Kinben-Electronics-Team/Kinben-Unified-Parts-Reference-System/.agent-work/task-0.3-integration.md

# TASK 0.3: SYSTEM INTEGRATION AUDIT - Assembly-System-Component Relationships

## Systems Tab HTML Structure (Lines 867-945)

### System Form Elements
- **Lines 872-888**: Metadata form (name, version, status, description)
- **Lines 895-921**: System items form
  - Item type selector: assembly/mechanical/printed3d/cable/system
  - Dynamic item dropdown (populated by `updateSystemItemOptions()`)
  - Quantity input (minimum 1)
  - Add Item button

### System Display Elements
- **Line 923**: `<div id="system-items">` - Current system items container
- **Lines 925-928**: Action buttons (Add System, Export CSV)
- **Line 930**: Search box for systems filtering
- **Lines 932-944**: Systems table with sortable columns

## Systems JavaScript Function Architecture

### Core System Management
- **`addSystemItem()`**: Adds items to current system-in-progress
- **`removeSystemItem(index)`**: Removes items from current system
- **`renderSystemItems()`**: Displays current system items during creation
- **`addSystem()`**: Saves complete system to `data.systems` array
- **`updateSystemItemOptions()`**: Populates item dropdown based on selected type

### System Display & Interaction
- **`renderSystems()`**: Renders all systems in main table
- **`sortSystems(column)`**: Sorts systems table by specified column
- **`filterSystems()`**: Search filter functionality
- **`exportSystems()`**: CSV export for systems data

## Three-Tier Architecture Data Flow

```
TIER 1: Components (KPN-based identification)
├── Electronic components (resistors, capacitors, ICs, etc.)
├── Mechanical parts (enclosures, screws, standoffs)
├── 3D-printed parts (custom housings, brackets)
└── Cable assemblies (harnesses, connectors)
    ↓ Referenced by KPN strings
    
TIER 2: Assemblies (Name-based identification)  
├── PCB assemblies with BOMs (component lists)
├── Cable assemblies (connector + wire specifications)
└── Mechanical assemblies (hardware groupings)
    ↓ Referenced by name strings
    
TIER 3: Systems (Name-based hierarchy)
├── Product-level systems (complete devices)
├── Sub-systems (functional blocks)
└── System-of-systems (nested hierarchies)
```

## System Item Types and Referencing Mechanisms

### Five System Item Types
1. **assembly**: References `data.assemblies` by name matching
2. **mechanical**: References components where `category='mechanical'` by KPN
3. **printed3d**: References components where `category='printed3d'` by KPN  
4. **cable**: References components where `category='cable'` by KPN
5. **system**: References other systems by name (enables hierarchical nesting)

### Reference Resolution Logic
```javascript
// Assembly references (by name)
assembly = data.assemblies.find(a => a.name === itemValue)

// Component references (by KPN)  
component = data.components.find(c => c.kpn === itemValue)

// System references (by name - hierarchical)
system = data.systems.find(s => s.name === itemValue)
```

## System Data Structure

### Complete System Object
```javascript
system = {
    name: "IoT Environmental Monitor",        // Unique system identifier
    version: "v1.0",                         // Version tracking
    status: "Active",                        // Active/Inactive status
    description: "Complete monitoring system", // System purpose
    items: [                                 // Array of system items
        {
            type: "assembly",                // Item type classifier
            value: "Main Controller Board", // Assembly name reference
            name: "Main Controller Board",  // Display name
            version: "v2.1",               // Assembly version (for display)
            quantity: 1                     // Quantity in system
        },
        {
            type: "mechanical",             // Component-based item
            value: "MEC-ENC-001",          // Component KPN reference
            name: "MEC-ENC-001",           // Component KPN (display)
            version: "Aluminum Enclosure", // Component description
            quantity: 1                    // Quantity in system
        }
    ],
    dateAdded: "2025-01-15T10:30:00.000Z"   // Creation timestamp
}
```

### Backward Compatibility Handling
- **Legacy Format**: `system.pcbs` array (deprecated)
- **Current Format**: `system.items` array
- **Migration**: Automatic conversion during data load
- **Display**: Handles both formats transparently

## Component-Assembly Relationship

### Assembly BOM Structure
```javascript
assembly = {
    name: "Main Controller Board",
    version: "v2.1", 
    status: "Active",
    description: "ARM-based controller",
    bom: [                              // Bill of Materials
        {
            kpn: "RES-STD-001",         // Component KPN reference
            componentName: "10kΩ Resistor", // Resolved component name
            quantity: 4,                // Quantity per assembly
            refdes: "R1,R2,R3,R4"      // Reference designators
        },
        {
            kpn: "CAP-CER-001",
            componentName: "100nF Capacitor",
            quantity: 2,
            refdes: "C1,C2"
        }
    ]
}
```

### Component Validation in BOMs
- **KPN Cross-Reference**: BOM items validate against `data.components`
- **CSV Import Validation**: Papa Parse system checks KPN existence
- **Missing KPN Handling**: Import preview shows validation errors
- **Real-time Updates**: Component changes reflect in assembly displays

## Assembly-System Relationship

### System Assembly References
```javascript
// System references assembly by name
systemItem = {
    type: "assembly",
    value: "Main Controller Board",    // Must match assembly.name exactly
    name: "Main Controller Board",     // Display name (same as value)
    version: "v2.1",                  // Assembly version (for display)
    quantity: 2                       // Quantity of this assembly in system
}

// Lookup mechanism
referencedAssembly = data.assemblies.find(a => a.name === systemItem.value)
```

### Assembly Selection Logic
- **Active Only**: Only assemblies with `status: "Active"` appear in dropdown
- **Name-based**: References use assembly name (not ID or KPN)
- **Version Display**: Assembly version shown for reference but not part of lookup
- **Quantity Management**: System-level quantities independent of assembly BOMs

## Data Storage and Persistence

### localStorage Structure
**Storage Key**: `'kinben-simple-data'`
```javascript
data = {
    components: [                       // Component library (KPN-indexed)
        { kpn: "RES-STD-001", category: "resistors", ... },
        { kpn: "CAP-CER-001", category: "capacitors", ... }
    ],
    assemblies: [                       // Assembly definitions (name-indexed)
        { name: "Main Controller", bom: [...], ... },
        { name: "Power Supply", bom: [...], ... }
    ],
    systems: [                          // System hierarchy (name-indexed)
        { name: "IoT Monitor", items: [...], ... },
        { name: "Control System", items: [...], ... }
    ],
    vendors: ["Mouser", "Digi-Key", ...]  // Vendor dropdown options
}
```

### CSV Integration Status
**Current CSV Support**:
- ✅ **Components**: Full read/write via 16 CSV files in `csvFileMap`
- ❌ **Assemblies**: Export only (`exportAssemblies()` function)
- ❌ **Systems**: Export only (`exportSystems()` function)

**Missing CSV Files**:
- No `ASSEMBLIES.csv` in `csvFileMap` 
- No `SYSTEMS.csv` in `csvFileMap`
- Systems and Assemblies persist to localStorage only

## Integration Validation Points

### System Item Validation
1. **Type Validation**: Ensures item type matches available options
2. **Reference Validation**: Checks existence of referenced assemblies/components
3. **Status Validation**: Only active assemblies/components selectable
4. **Quantity Validation**: Minimum 1, integer values only

### Cross-Reference Integrity
```javascript
// Assembly → Component validation (in BOM)
bomItem.kpn exists in data.components.map(c => c.kpn)

// System → Assembly validation (in items)
systemItem.value exists in data.assemblies.filter(a => a.status === 'Active').map(a => a.name)

// System → Component validation (mechanical/3d/cable items)
systemItem.value exists in data.components.filter(c => c.category === itemType).map(c => c.kpn)
```

### Data Migration and Compatibility
- **Automatic Migration**: Converts legacy `system.pcbs` to `system.items`
- **Version Handling**: Maintains version info across all tiers
- **Status Propagation**: Inactive items excluded from selection but preserved in data
- **Export Compatibility**: CSV exports handle both legacy and current formats

## System Hierarchy Architecture

### Hierarchical Nesting Support
```javascript
// System can contain other systems
systemItem = {
    type: "system",
    value: "Sub-Control Module",       // References another system by name
    name: "Sub-Control Module", 
    version: "v1.3",
    quantity: 1
}
```

### Circular Reference Prevention
- **Current Status**: No automatic circular reference detection
- **Manual Prevention**: User responsibility to avoid circular references
- **Future Enhancement**: Validation system needed for complex hierarchies

## Assessment Summary

**Current Integration Status**:
- ✅ **Component-Assembly**: Full KPN-based referencing with CSV import validation
- ✅ **Assembly-System**: Complete name-based referencing with active status filtering
- ✅ **Data Persistence**: Unified localStorage system with backward compatibility
- ✅ **Export Capabilities**: CSV export for all data types
- ⚠️ **CSV Sync**: Limited to components only (assemblies/systems localStorage only)
- ⚠️ **Circular References**: No validation for system hierarchies

**Architecture Strengths**:
- Clear three-tier hierarchy with distinct referencing mechanisms
- Flexible item type system supporting diverse product structures
- Robust validation and error handling at integration points
- Backward compatibility with legacy data formats
- Real-time updates across all integration points

**Ready for Enhancement**: 
- Modular architecture supports easy extension to new item types
- Clear separation of concerns between tiers
- Extensible validation system for new requirements
- Foundation prepared for advanced hierarchy features

**No Code Modifications Made**: Assessment only - all functionality remains unchanged.
