Kinben-Electronics-Team/Kinben-Unified-Parts-Reference-System/.agent-work/task-1.3-data-model.md

# TASK 1.3: EXTEND DATA MODEL

## Implementation Progress

**Objective**: Update assembly objects to include type and type-specific data  
**Status**: COMPLETE - All code changes implemented  
**Date**: 2025-07-31  

## Code Changes Made

### Data Collection Enhancement (Lines 3377-3379)
**Function**: `addAssembly()` - Extended to collect cable-specific data

```javascript
// Collect cable-specific data if cable assembly
const cableLength = document.getElementById('cableLength').value;
const cableType = document.getElementById('cableType').value;
```

**Features**:
- Collects cable length and type values from form fields
- Values collected regardless of assembly type (form handles visibility)
- Prepared for conditional storage based on assembly type

### Extended Assembly Object Structure (Lines 3386-3404)
**Updated Data Model**: Assembly objects now include type-specific data containers

```javascript
const assembly = {
    name,
    type: assemblyType,  // 'pcb' or 'cable'
    version,
    status,
    description,
    // Type-specific data
    pcbData: assemblyType === 'pcb' ? {
        bom: [...currentBOM]
    } : null,
    cableData: assemblyType === 'cable' ? {
        length: cableLength ? parseInt(cableLength) : null,
        cableType: cableType || null,
        bom: [...currentBOM]
    } : null,
    // Legacy field for backward compatibility
    bom: [...currentBOM],
    dateAdded: new Date().toISOString().split('T')[0]
};
```

**Data Model Features**:
- **Type-Specific Storage**: PCB data stored in `pcbData`, cable data in `cableData`
- **Conditional Creation**: Only relevant data object created based on assembly type
- **Data Validation**: Cable length converted to integer, handles empty values
- **Backward Compatibility**: Legacy `bom` field maintained for existing code
- **BOM Duplication**: BOM stored in both type-specific and legacy locations

### Data Migration Logic (Lines 1903-1919)
**Function**: `loadData()` - Automatic migration for existing assemblies

```javascript
// Migrate assemblies to include type field (default to PCB)
if (data.assemblies) {
    let migrationNeeded = false;
    data.assemblies.forEach(assembly => {
        if (!assembly.type) {
            assembly.type = 'pcb'; // Default existing assemblies to PCB type
            assembly.pcbData = {
                bom: assembly.bom || []
            };
            assembly.cableData = null;
            migrationNeeded = true;
        }
    });
    if (migrationNeeded) {
        saveData();
    }
}
```

**Migration Features**:
- **Automatic Detection**: Identifies assemblies without type field
- **PCB Default**: Existing assemblies default to PCB type (safest assumption)
- **Data Structure Creation**: Creates pcbData object with existing BOM
- **Null Cable Data**: Sets cableData to null for migrated PCB assemblies
- **Efficient Saving**: Only saves data if migration was actually needed
- **One-Time Process**: Migration runs once per legacy assembly

## Data Structure Specifications

### PCB Assembly Data Structure
```javascript
{
    name: "Main Controller Assembly",
    type: "pcb",
    version: "v1.0",
    status: "Active",
    description: "ARM-based controller board",
    pcbData: {
        bom: [...bomItems]  // Array of BOM items
    },
    cableData: null,
    bom: [...bomItems],  // Legacy compatibility
    dateAdded: "2025-07-31"
}
```

### Cable Assembly Data Structure
```javascript
{
    name: "Main Power Cable",
    type: "cable",
    version: "v1.0", 
    status: "Active",
    description: "Power distribution cable assembly",
    pcbData: null,
    cableData: {
        length: 500,           // Length in mm (integer)
        cableType: "18 AWG",   // Cable type specification
        bom: [...bomItems]     // Array of BOM items (connectors, etc.)
    },
    bom: [...bomItems],  // Legacy compatibility
    dateAdded: "2025-07-31"
}
```

### Legacy Assembly (Migrated) Structure
```javascript
{
    name: "Legacy PCB Assembly",
    type: "pcb",           // Added by migration
    version: "v1.0",
    status: "Active", 
    description: "Pre-migration assembly",
    pcbData: {             // Added by migration
        bom: [...bomItems] // Copied from legacy bom field
    },
    cableData: null,       // Added by migration
    bom: [...bomItems],    // Original legacy field preserved
    dateAdded: "2025-07-30"
}
```

## Validation Requirements

### Success Criteria Progress
- [x] New assembly objects include type field
- [x] Type-specific data stored appropriately (pcbData/cableData)
- [x] Existing assemblies migrated successfully (default to PCB)
- [x] CSV sync includes new fields (handled by saveData)
- [x] Data integrity maintained throughout

## Technical Implementation Features

### Type-Specific Data Storage
- **PCB Assemblies**: BOM stored in `pcbData.bom`
- **Cable Assemblies**: BOM + cable specs stored in `cableData`
- **Efficient Storage**: Only relevant data object created per type
- **Data Validation**: Cable length parsed as integer with null fallback

### Backward Compatibility Strategy
- **Legacy BOM Field**: Maintained in all assemblies for existing code
- **Migration Logic**: Automatically updates existing data structures
- **Default Behavior**: Unknown assemblies default to PCB type
- **Preservation**: All existing data preserved during migration

### Data Persistence Integration
- **localStorage Sync**: Extended data model saved to localStorage
- **CSV Integration**: Type-specific data included in CSV exports
- **Migration Persistence**: Migration changes saved automatically
- **Performance**: Migration only runs when needed

## Migration Testing Scenarios

### Scenario 1: Fresh Installation
- **Behavior**: New assemblies created with full type-specific data model
- **PCB Assembly**: Creates pcbData object, cableData null
- **Cable Assembly**: Creates cableData object, pcbData null

### Scenario 2: Existing Data Migration
- **Detection**: Assemblies without type field automatically detected
- **Default Assignment**: All legacy assemblies become PCB type
- **Data Migration**: BOM data moved to pcbData.bom structure
- **Preservation**: Original bom field maintained for compatibility

### Scenario 3: Mixed Data Environment
- **Handling**: New and migrated assemblies coexist seamlessly
- **Consistency**: All assemblies have consistent data structure after migration
- **Functionality**: Both old and new assemblies work with existing code

## Status: TASK 1.3 COMPLETE
✅ Assembly objects extended with type field  
✅ Type-specific data containers implemented (pcbData/cableData)  
✅ Data collection from form fields integrated  
✅ Migration logic for existing assemblies implemented  
✅ Backward compatibility maintained with legacy bom field  
✅ Data persistence and CSV sync compatible  
✅ One-time migration process efficient and safe  
✅ Ready for Task 1.4 - Enhance BOM CSV Import
