Kinben-Electronics-Team/Kinben-Unified-Parts-Reference-System/.agent-work/task-2.2-mother-view.md

# TASK 2.2: IMPLEMENT MOTHER VIEW COMPONENTS

## Implementation Progress

**Objective**: Add manual component entry at assembly level for enclosures, hardware, and other components  
**Status**: COMPLETE - Assembly-level component system implemented  
**Date**: 2025-07-31  

## Code Changes Made

### Assembly Form UI Enhancement (Lines 940-971)
**Location**: Added after BOM CSV Import section, before action buttons

```html
<h3>🏗️ Assembly-Level Components</h3>
<p>Add enclosures, hardware, and other components needed at the assembly level</p>

<div class="form-grid">
    <div class="form-group">
        <label>Component Type</label>
        <select id="mother-type" onchange="updateMotherItemOptions()">
            <option value="">Select Component Type</option>
            <option value="enclosure">Enclosure/Housing</option>
            <option value="hardware">Hardware (Screws, Standoffs)</option>
            <option value="mounting">Mounting Components</option>
            <option value="cable">External Cables</option>
            <option value="other">Other</option>
        </select>
    </div>
    <div class="form-group">
        <label>Component KPN</label>
        <select id="mother-kpn" onchange="updateMotherComponentName()">
            <option value="">Select Component Type First</option>
        </select>
    </div>
    <div class="form-group">
        <label>Quantity</label>
        <input type="number" id="mother-quantity" min="1" value="1">
    </div>
    <div class="form-group">
        <label>Notes</label>
        <input type="text" id="mother-notes" placeholder="Optional notes">
    </div>
</div>
<button class="btn btn-secondary" onclick="addMotherComponent()">Add Assembly Component</button>
```

**UI Design Features**:
- **Separate Section**: Clearly distinguished from PCB/Cable BOM components
- **Component Type Categories**: Enclosure, hardware, mounting, cables, other
- **Dynamic KPN Dropdown**: Filters components based on selected type
- **Form Validation**: Required fields with proper input types
- **Live Preview**: Shows added components in real-time

### Global State Management (Line 3437)
**Variable**: `currentMotherComponents` array for tracking assembly-level components

```javascript
let currentBOM = [];
let currentMotherComponents = [];
```

### Component Type Mapping Logic (Lines 4094-4137)
**Function**: `updateMotherItemOptions()` - Maps component types to relevant categories

```javascript
function updateMotherItemOptions() {
    const type = document.getElementById('mother-type').value;
    const kpnSelect = document.getElementById('mother-kpn');
    
    // Map mother component types to component categories
    const categoryMap = {
        'enclosure': ['mechanical'],
        'hardware': ['mechanical', 'hardware'],
        'mounting': ['mechanical', 'hardware'],
        'cable': ['connectors', 'cable'],
        'other': ['mechanical', 'hardware', 'connectors']
    };
    
    const relevantCategories = categoryMap[type] || [];
    
    // Filter and populate components from existing library
    // ... DOM table extraction logic ...
}
```

**Intelligent Filtering**:
- **Enclosure**: Shows mechanical components (housings, cases)
- **Hardware**: Shows mechanical and hardware components (screws, standoffs)
- **Mounting**: Shows mounting-related components
- **Cable**: Shows connectors and cable-related items
- **Other**: Shows broad range of relevant components

### Mother Component Management (Lines 4140-4225)
**Core Functions**: Add, render, and remove assembly-level components

```javascript
function addMotherComponent() {
    const type = document.getElementById('mother-type').value;
    const kpn = document.getElementById('mother-kpn').value;
    const quantity = parseInt(document.getElementById('mother-quantity').value);
    const notes = document.getElementById('mother-notes').value;
    
    // Validation and component object creation
    const motherComponent = {
        type,
        kpn,
        componentName,
        quantity,
        notes
    };
    
    currentMotherComponents.push(motherComponent);
    renderMotherComponents();
    // Clear form fields
}

function renderMotherComponents() {
    // Display components in card-based layout
    // Real-time preview with remove functionality
}

function removeMotherComponent(index) {
    currentMotherComponents.splice(index, 1);
    renderMotherComponents();
}
```

### Data Model Extension (Lines 3508, 3528-3529)
**Assembly Object**: Extended to include mother components

```javascript
// Updated validation logic
if (!name || !assemblyType || !version || (currentBOM.length === 0 && currentMotherComponents.length === 0)) {
    alert('Please fill in assembly details and add at least one BOM item or assembly component');
    return;
}

// Extended assembly data structure
const assembly = {
    name,
    type: assemblyType,
    version,
    status,
    description,
    // Type-specific data
    pcbData: assemblyType === 'pcb' ? {
        bom: [...currentBOM]
    } : null,
    cableData: assemblyType === 'cable' ? {
        length: cableLength ? parseInt(cableLength) : null,
        cableType: cableType || null,
        bom: [...currentBOM]
    } : null,
    // Assembly-level components (mother view)
    motherComponents: [...currentMotherComponents],
    // Legacy field for backward compatibility
    bom: [...currentBOM],
    dateAdded: new Date().toISOString().split('T')[0]
};
```

**Key Features**:
- **Separate Storage**: Mother components stored independently from BOM
- **Validation Logic**: Assembly valid with either BOM items OR mother components
- **Backward Compatibility**: Legacy BOM field maintained
- **Type Integration**: Works with both PCB and Cable assembly types

### Enhanced Display System (Lines 4043-4066)
**Assembly Detail View**: Shows both mother and child components hierarchically

```javascript
bomRow.innerHTML = `
    <td colspan="5">
        <div class="bom-detail-container">
            <h4>Assembly Details - ${assembly.name}</h4>
            ${assembly.motherComponents && assembly.motherComponents.length > 0 ? `
                <div class="mother-components-section">
                    <h5>🏗️ Assembly-Level Components</h5>
                    <div class="bom-items-list">
                        ${renderAssemblyMotherComponents(assembly.motherComponents)}
                    </div>
                </div>
            ` : ''}
            ${assembly.bom && assembly.bom.length > 0 ? `
                <div class="bom-components-section">
                    <h5>🔧 PCB/Cable Components</h5>
                    <div class="bom-items-list">
                        ${renderAssemblyBOMItems(assembly.bom)}
                    </div>
                </div>
            ` : ''}
        </div>
    </td>
`;
```

### Mother Component Rendering (Lines 4227-4251)
**Function**: `renderAssemblyMotherComponents()` - Display mother components in assembly detail view

```javascript
function renderAssemblyMotherComponents(motherComponents) {
    let html = '<div class="bom-items-grid">';
    motherComponents.forEach(item => {
        html += `
            <div class="bom-item-card mother-component-card">
                <div class="bom-item-header">
                    <strong>${item.componentName || item.kpn}</strong>
                    <span class="quantity-badge mother-quantity-badge">Qty: ${item.quantity}</span>
                </div>
                <div class="bom-item-details">
                    <div><span class="component-type-badge">${item.type.charAt(0).toUpperCase() + item.type.slice(1)}</span></div>
                    <div>KPN: ${item.kpn}</div>
                    ${item.notes ? `<div class="notes">Notes: ${item.notes}</div>` : ''}
                </div>
            </div>
        `;
    });
    html += '</div>';
    return html;
}
```

### Quantity Rollup Integration (Line 4033)
**Assembly Summary**: Combined count of BOM and mother components

```javascript
<td>${(assembly.bom?.length || 0) + (assembly.motherComponents?.length || 0)} items</td>
```

**Smart Counting**:
- **Total Items**: Shows combined count of child + mother components
- **Null Safety**: Handles assemblies without mother components gracefully
- **Backward Compatibility**: Works with legacy assemblies

### Form Management Integration (Lines 3546-3550)
**Form Reset**: Clears both BOM and mother components

```javascript
currentBOM = [];
currentMotherComponents = [];
renderBOMItems();
renderMotherComponents();
toggleAssemblyFields(); // Reset field visibility
```

### CSS Styling System (Lines 401-464)
**Visual Design**: Complete styling for mother component system

```css
.mother-component-row {
    display: flex;
    justify-content: space-between;
    align-items: center;
    padding: 12px;
    border: 1px solid #dee2e6;
    border-radius: 4px;
    margin-bottom: 8px;
    background: #f8f9fa;
}

.component-type-badge {
    background: #28a745;
    color: white;
    padding: 2px 6px;
    border-radius: 3px;
    font-size: 11px;
    font-weight: bold;
}

.mother-component-card {
    border-left: 4px solid #28a745;
}

.mother-quantity-badge {
    background: #28a745;
}
```

**Design Language**:
- **Green Theme**: Mother components use green accents (#28a745)
- **Visual Distinction**: Different colors from child components (blue)
- **Card Layout**: Consistent with existing BOM item cards
- **Type Badges**: Clear identification of component types

## User Experience Design

### Assembly Creation Workflow
**Enhanced Assembly Form**:
1. **Basic Assembly Info**: Name, type, version, description
2. **Child Components**: PCB/Cable BOM items (existing functionality)
3. **Mother Components**: Assembly-level items (new functionality)
4. **Validation**: Requires at least one type of component
5. **Preview**: Real-time display of both component types

### Hierarchical Display System
**Two-Level Component Structure**:
```
📋 IoT Controller Assembly v1.0               [▶] 8 items    Active
└─ 🏗️ Assembly-Level Components (3 items)
   ├─ 📦 Aluminum Enclosure               Qty: 1    (Hardware)
   ├─ 🔩 M3x8 Socket Head Screws          Qty: 4    (Hardware)  
   └─ 🔌 Power Cable Assembly             Qty: 1    (Cable)
└─ 🔧 PCB/Cable Components (5 items)
   ├─ 💾 ARM Cortex-M4                    Qty: 1    R1,R2,R3,R4
   ├─ 🔌 10kΩ Resistors                   Qty: 4    C1,C2
   └─ ⚡ 100nF Capacitors                 Qty: 2    J1
```

### Component Type Categories
**Intelligent Categorization**:
- **Enclosure/Housing**: Cases, housings, protective covers
- **Hardware**: Screws, standoffs, spacers, washers
- **Mounting**: Brackets, clips, mounting hardware
- **External Cables**: Power cables, data cables, harnesses
- **Other**: Miscellaneous assembly-level components

## Technical Implementation Features

### Data Separation Architecture
**Clear Separation of Concerns**:
- **Child Components**: Technical components mounted on PCBs/cables
- **Mother Components**: Physical assembly and mounting components
- **Data Storage**: Separate arrays maintain distinct component types
- **Display Logic**: Hierarchical rendering shows relationship clearly

### Component Filtering Intelligence
**Smart Component Suggestions**:
- **Type-Aware Filtering**: Only shows relevant components per category
- **Real Component Data**: Uses actual KPNs from component library
- **Dynamic Updates**: Component list updates when type selection changes
- **Fallback Handling**: Graceful handling when no components match

### Form State Management
**Robust Form Handling**:
- **Independent State**: Mother components don't interfere with BOM workflow
- **Form Validation**: Smart validation allows either BOM or mother components
- **Reset Behavior**: Proper cleanup of all form states
- **Error Handling**: Clear validation messages for missing fields

### Integration with Existing Systems
**Seamless Integration**:
- **Assembly Type System**: Works with both PCB and Cable assemblies
- **CSV Integration**: Mother components included in data persistence
- **Search/Filter**: Assembly search includes mother component counts
- **Export System**: Mother components included in assembly exports

## User Interface Enhancements

### Visual Hierarchy
**Clear Information Architecture**:
- **Section Headers**: Distinct icons and titles for each component type
- **Color Coding**: Green theme for mother components vs blue for child
- **Card Layout**: Consistent design language with existing UI
- **Progressive Disclosure**: Expandable details maintain clean overview

### Interaction Design
**Intuitive User Flow**:
- **Type-First Selection**: Choose category before selecting specific component
- **Real-Time Preview**: See components as they're added
- **Easy Removal**: One-click removal of unwanted components
- **Form Feedback**: Clear validation and success indicators

## Data Model Impact

### Assembly Data Structure
**Extended Schema**:
```javascript
assembly = {
    name: "IoT Controller Assembly",
    type: "pcb",
    version: "v1.0",
    motherComponents: [
        {
            type: "enclosure",
            kpn: "MEC-ENC-001", 
            componentName: "Aluminum Case",
            quantity: 1,
            notes: "IP65 rated"
        },
        {
            type: "hardware",
            kpn: "MEC-SCR-003",
            componentName: "M3x8 Socket Head Screws",
            quantity: 4,
            notes: "Case mounting"
        }
    ],
    pcbData: {
        bom: [...childComponents]
    },
    // Legacy compatibility maintained
    bom: [...childComponents]
}
```

### Quantity Calculations
**Integrated Counting**:
- **Assembly Summary**: Total count includes both component types
- **Hierarchical Display**: Separate counts for each component level
- **Export Integration**: Full component manifest includes all types
- **System Rollups**: Higher-level systems can roll up both component types

## Status: TASK 2.2 COMPLETE
✅ Assembly-level component entry system implemented  
✅ UI section with component type categorization added  
✅ Mother components stored separately from child BOM  
✅ Hierarchical display shows both component levels  
✅ Quantity rollups include both mother and child components  
✅ Smart component filtering by type category  
✅ Complete CSS styling with visual distinction  
✅ Form validation and state management integrated  
✅ Data model extended with backward compatibility  
✅ Ready for Task 2.3 - Quantity Calculation Engine
