Kinben-Electronics-Team/Kinben-Unified-Parts-Reference-System/.agent-work/system-status-alert.md

# 🚨 SYSTEM STATUS ALERT - BROKEN FUNCTIONALITY

## Current Status
**Date**: 2025-07-31  
**Task**: 2.3 - Build Quantity Calculation Engine  
**Status**: ❌ **SYSTEM BROKEN** - Implementation has caused functionality issues  

## Issue Description
The implementation of Task 2.3 (Quantity Calculation Engine) has broken system functionality. The code changes may have introduced:
- JavaScript errors preventing proper page functionality
- Broken references to DOM elements or functions
- Issues with the expanded calculation logic
- Problems with new system detail views

## Last Working State
- ✅ Task 2.1: Child View BOM - Working
- ✅ Task 2.2: Mother View Components - Working  
- ❌ Task 2.3: Quantity Calculation Engine - **BROKE SYSTEM**

## Changes Made in Task 2.3
1. **Added modular calculation functions** (Lines 4347-4500)
   - `calculateAssemblyQuantities()`
   - `calculateSystemTotals()`
   - `getComponentTotalAcrossAssemblies()`

2. **Enhanced assembly detail view** (Lines 4319-4345)
   - Added `renderAssemblyQuantitySummary()`
   - Modified assembly detail display

3. **Enhanced systems table** (Lines 4502-4565)
   - Added expandable system details
   - Added `toggleSystemDetails()` function
   - Modified `renderSystems()` function

4. **Added new rendering functions** (Lines 4567-4653)
   - `renderSystemQuantitySummary()`
   - `renderSystemAssemblies()`
   - `renderConsolidatedComponents()`

5. **Added extensive CSS styling** (Lines 504-588)
   - Quantity summary styles
   - System card styles
   - Assembly breakdown styles

## Immediate Action Required
1. **Identify the specific error** causing system failure
2. **Debug JavaScript console** for error messages
3. **Test basic functionality** (page load, tab navigation, form submission)
4. **Consider rollback** if errors are too extensive
5. **Fix critical path** to restore basic functionality

## Recovery Options
1. **Incremental Rollback**: Remove most recent changes and re-add incrementally
2. **Targeted Fix**: Identify and fix specific breaking changes
3. **Staged Implementation**: Implement calculation engine in smaller, testable pieces

## Documentation Status
- ✅ Task 2.3 documentation completed
- ✅ Progress tracking updated
- ❌ System functionality verification FAILED

## Next Steps
1. **DEBUG SYSTEM** - Identify root cause of breakage
2. **RESTORE FUNCTIONALITY** - Fix or rollback breaking changes  
3. **TEST THOROUGHLY** - Verify system works before proceeding
4. **CONTINUE TASK 2.3** - Complete implementation without breaking system
5. **FOLLOW VALIDATION PROTOCOL** - Test after each change

---

**⚠️ CRITICAL**: System must be restored to working state before proceeding with any additional development.

**📋 COMMIT STATUS**: Changes should NOT be committed until system is restored and verified working.
