Kinben-Electronics-Team/Kinben-Unified-Parts-Reference-System/Kinben Basic Kicad Library/3d_models/HCS1206FTL500.stp

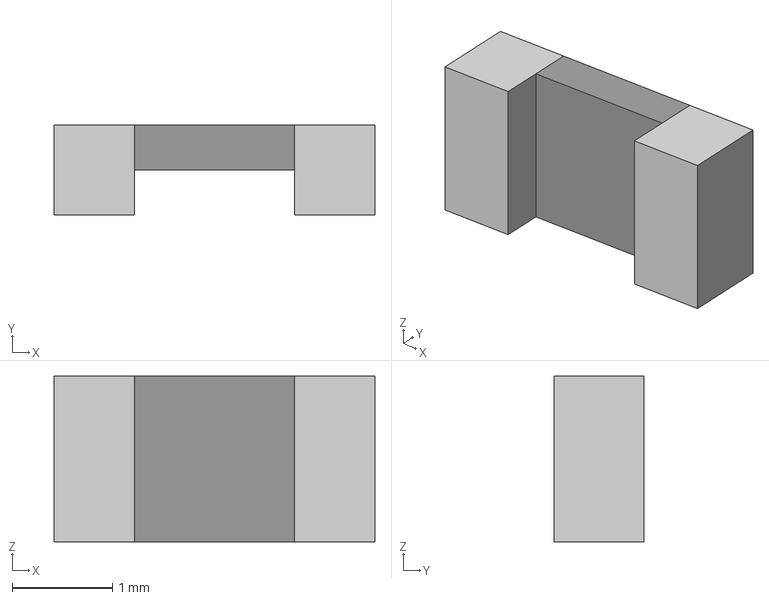
[picture p15: CAD file, 2025-07-21]
Kinben Basic Kicad Library/3d_models/HCS1206FTL500.stp
3.20 x 0.9 x 1.65 mm
