Kinben-Electronics-Team/Kinben-Unified-Parts-Reference-System/Kinben Basic Kicad Library/3d_models/S2B-PH-SM4-TB.stp

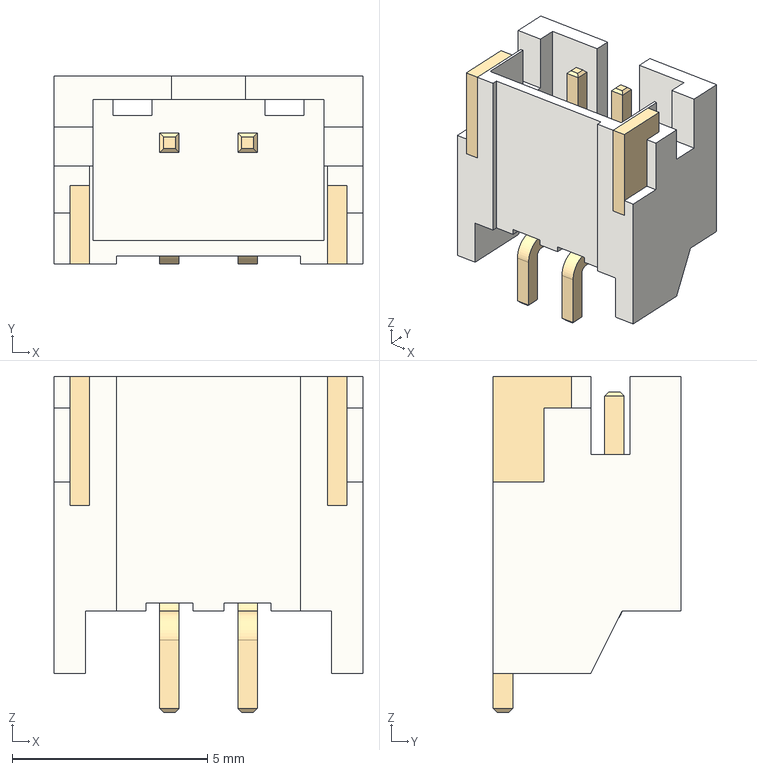
[picture p16: CAD file, 2025-07-21]
Kinben Basic Kicad Library/3d_models/S2B-PH-SM4-TB.stp
7.90 x 4.80 x 8.60 mm
