Kinben-Electronics-Team/Kinben-Unified-Parts-Reference-System/Kinben Basic Kicad Library/3d_models/RPE0009A.stp

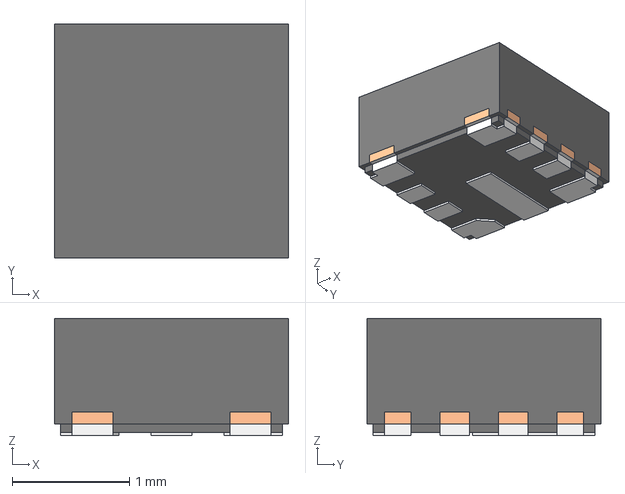
[picture p17: CAD file, 2025-07-21]
Kinben Basic Kicad Library/3d_models/RPE0009A.stp
2.00 x 2.00 x 1.00 mm
FRAME_AF0
MOLD_AF0
