Kinben-Electronics-Team/Kinben-Unified-Parts-Reference-System/Kinben Basic Kicad Library/3d_models/SOT1165D.step

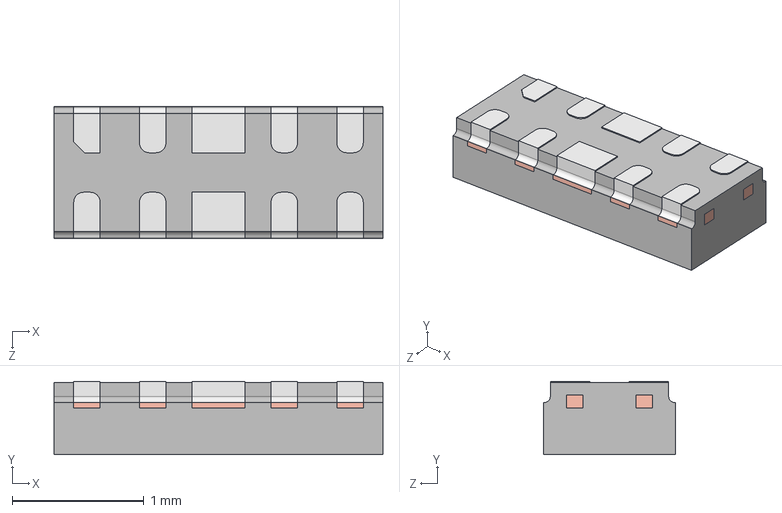
[picture p18: CAD file, 2025-07-21]
Kinben Basic Kicad Library/3d_models/SOT1165D.step
2.50 x 0.556 x 1.00 mm
SOT1165D LF
SOT1165D Mold body
