Kinben-Electronics-Team/Kinben-Unified-Parts-Reference-System/Kinben Basic Kicad Library/3d_models/SOT-23F.STEP

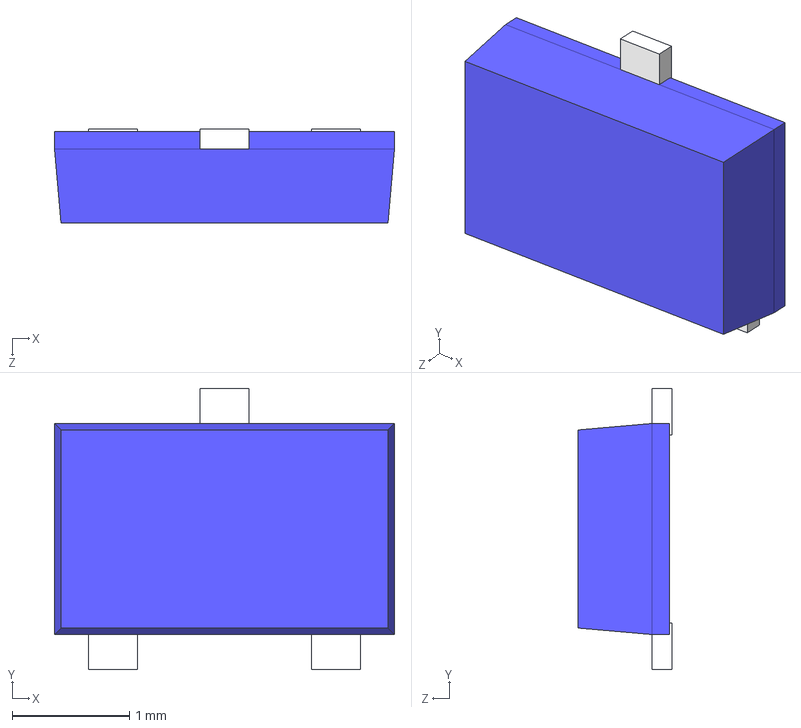
[picture p19: CAD file, 2025-07-21]
Kinben Basic Kicad Library/3d_models/SOT-23F.STEP
2.90 x 2.40 x 0.8 mm
