Kinben-Electronics-Team/Kinben-Unified-Parts-Reference-System/Kinben Basic Kicad Library/3d_models/SM1206XXC-IL.step

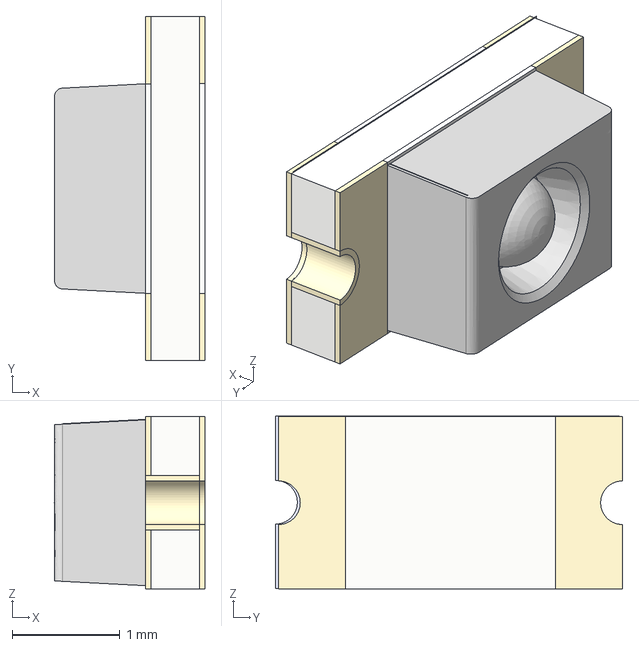
[picture p20: CAD file, 2025-07-21]
Kinben Basic Kicad Library/3d_models/SM1206XXC-IL.step
1.40 x 3.23 x 1.61 mm
