Kinben-Electronics-Team/Kinben-Unified-Parts-Reference-System/Kinben Basic Kicad Library/3d_models/TSQFP50P1200X1200X160-64N.step

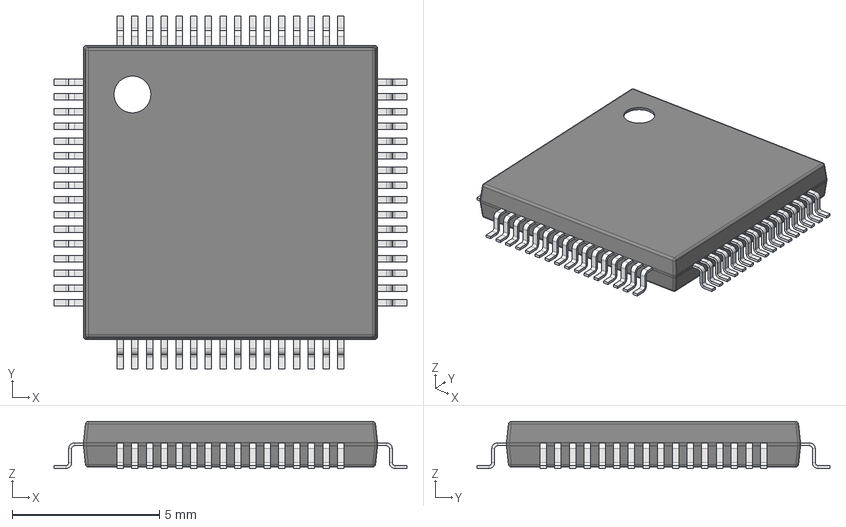
[picture p21: CAD file, 2025-07-21]
Kinben Basic Kicad Library/3d_models/TSQFP50P1200X1200X160-64N.step
12.0 x 12.0 x 1.60 mm
Leader x 64
