Kinben-Electronics-Team/Kinben-Unified-Parts-Reference-System/Kinben Basic Kicad Library/3d_models/SOP127P600-8N.step

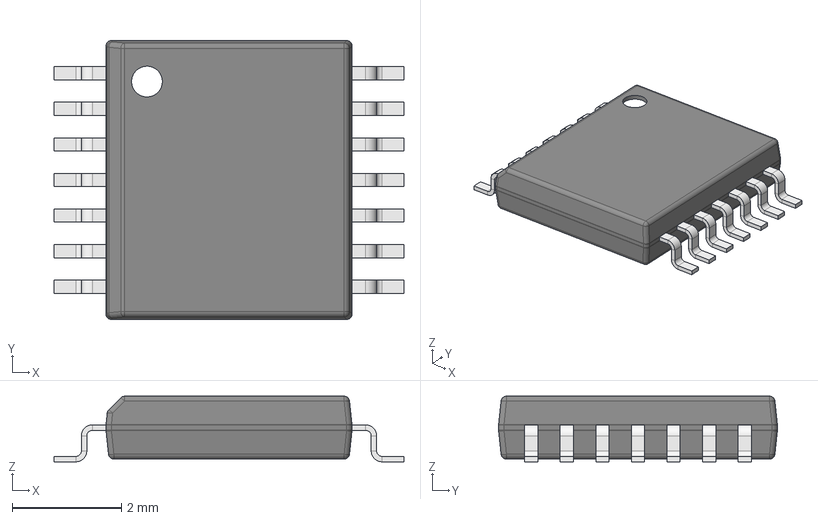
[picture p22: CAD file, 2025-07-21]
Kinben Basic Kicad Library/3d_models/SOP127P600-8N.step
6.40 x 5.10 x 1.20 mm
Leader x 14
