Kinben-Electronics-Team/Kinben-Unified-Parts-Reference-System/Kinben Basic Kicad Library/3d_models/SOT95P230X110-3N.step

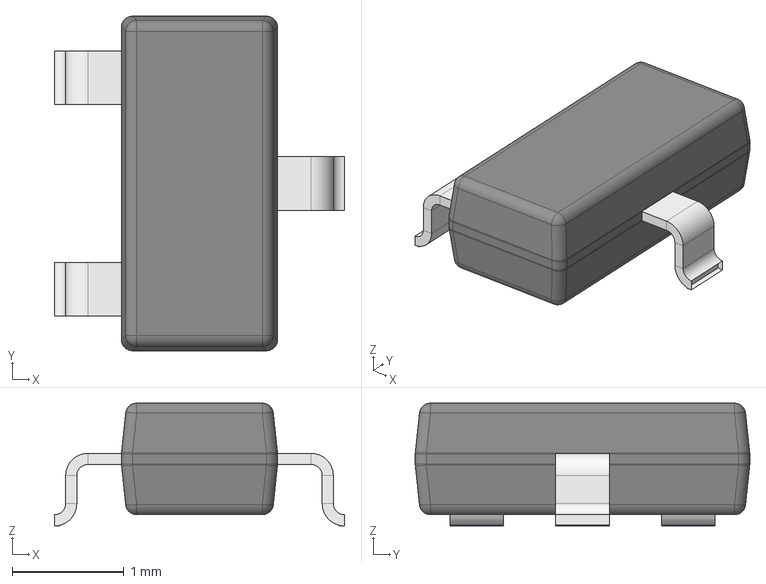
[picture p23: CAD file, 2025-07-21]
Kinben Basic Kicad Library/3d_models/SOT95P230X110-3N.step
2.60 x 3.00 x 1.10 mm
Leader x 3
