Kinben-Electronics-Team/Kinben-Unified-Parts-Reference-System/Kinben Basic Kicad Library/3d_models/SOT8009.stp

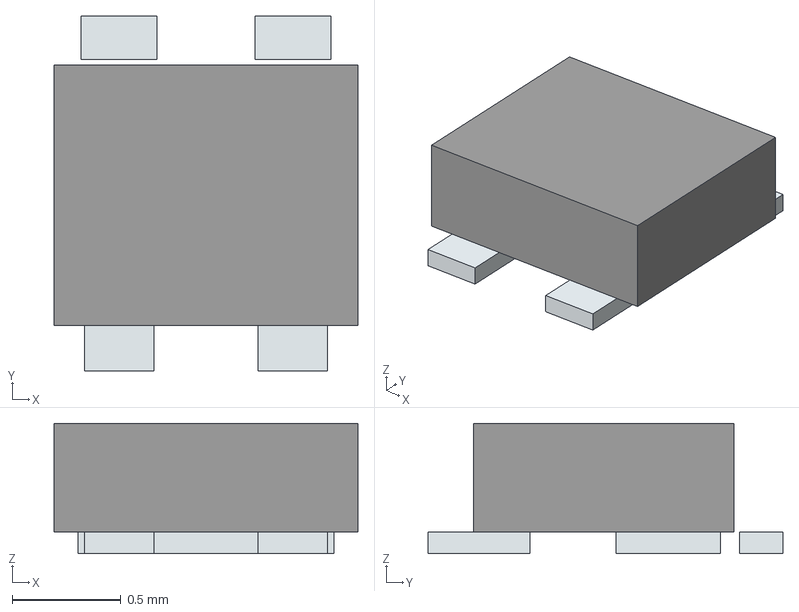
[picture p24: CAD file, 2025-07-21]
Kinben Basic Kicad Library/3d_models/SOT8009.stp
1.40 x 1.64 x 0.6 mm
Pins
