Kinben-Electronics-Team/Kinben-Unified-Parts-Reference-System/Kinben Basic Kicad Library/3d_models/XT60-PW-F.step

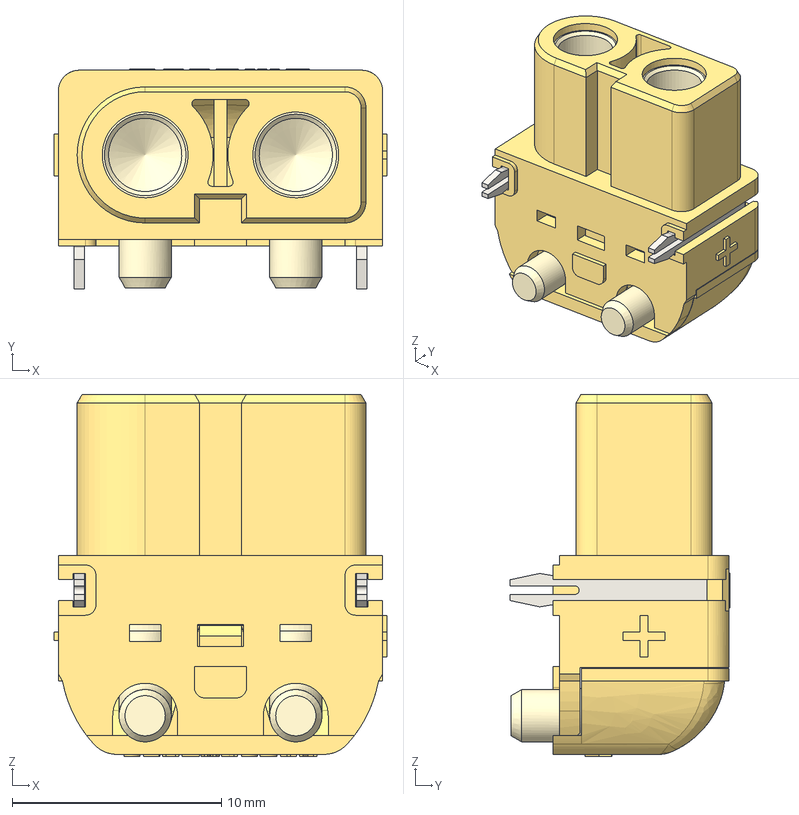
[picture p25: CAD file, 2025-07-21]
Kinben Basic Kicad Library/3d_models/XT60-PW-F.step
15.9 x 10.5 x 17.3 mm
XT60____-8______-UL-21155
XT60____-8____-21158 x 2
XT60PW-F20____-8-UL
XT60____-8________ x 2
