Kinben-Electronics-Team/Kinben-Unified-Parts-Reference-System/Kinben Basic Kicad Library/3d_models/SOT65P210X110-3N.step

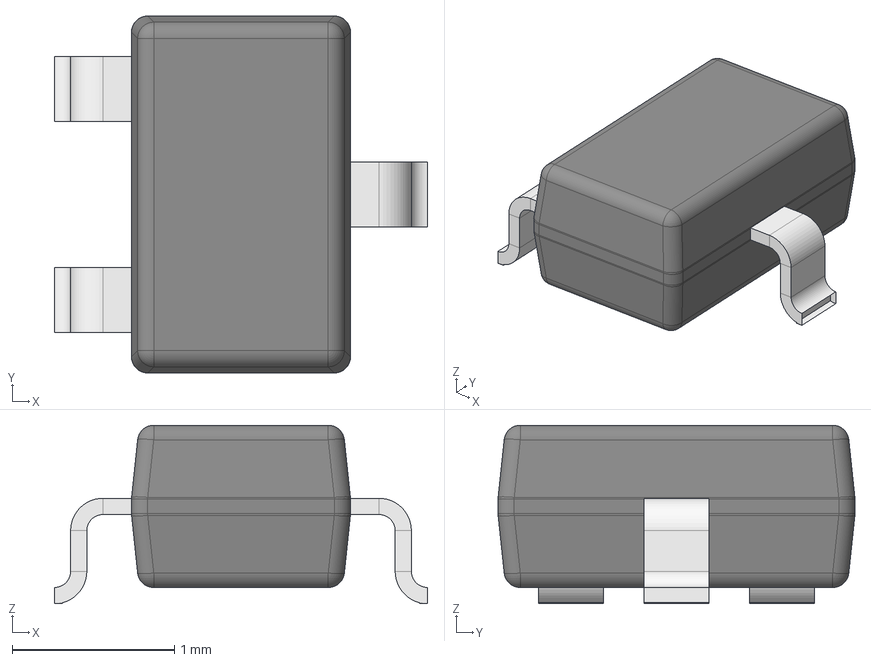
[picture p26: CAD file, 2025-07-21]
Kinben Basic Kicad Library/3d_models/SOT65P210X110-3N.step
2.30 x 2.20 x 1.10 mm
Leader x 3
