Kinben-Electronics-Team/Kinben-Unified-Parts-Reference-System/Kinben Basic Kicad Library/3d_models/XT60PW-M.STEP

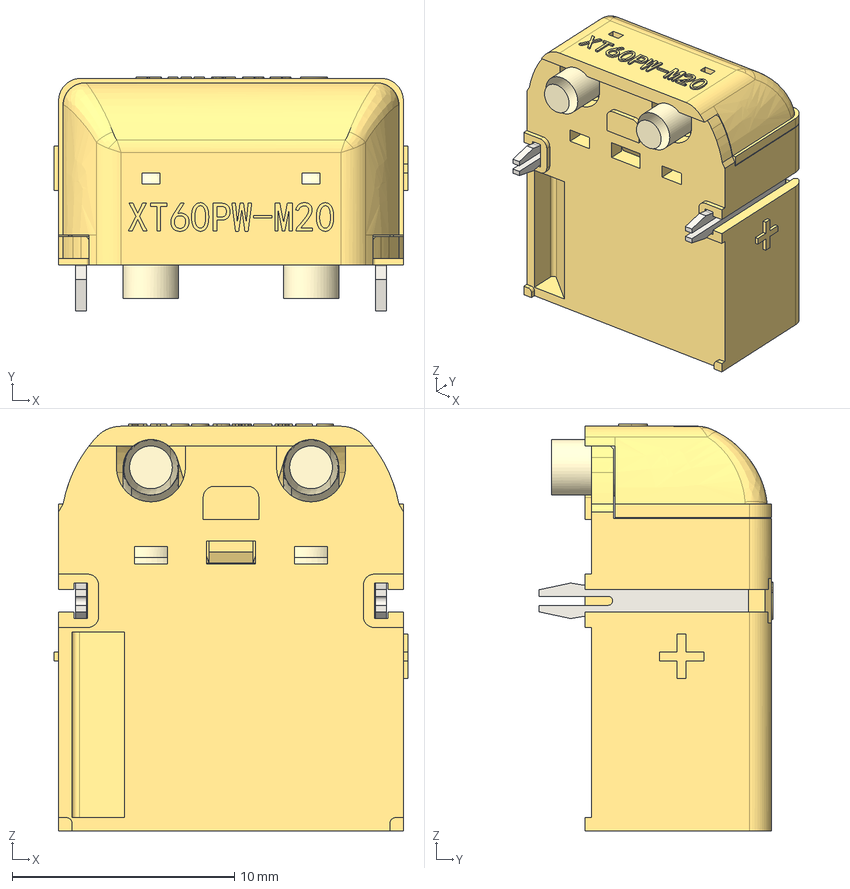
[picture p27: CAD file, 2025-07-21]
Kinben Basic Kicad Library/3d_models/XT60PW-M.STEP
15.9 x 10.5 x 18.3 mm
XT60____-8______-UL-21156
XT60____-8____-21157 x 2
XT60____-8________ x 2
XT60PW-M20____-8-UL
XT60-PW-F
