Kinben-Electronics-Team/Kinben-Unified-Parts-Reference-System/Kinben Basic Kicad Library/3d_models/Mounting_Wuerth_WA-SMSI-M2_H2mm_9774020243.step

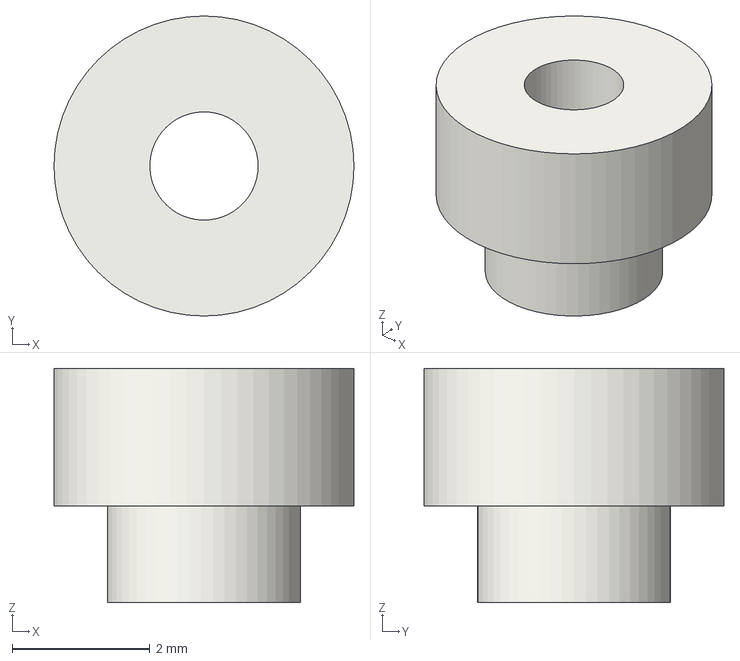
[picture p28: CAD file, 2025-07-21]
Kinben Basic Kicad Library/3d_models/Mounting_Wuerth_WA-SMSI-M2_H2mm_9774020243.step
4.35 x 4.35 x 3.40 mm
