Kinben-Electronics-Team/Kinben-Unified-Parts-Reference-System/Kinben Basic Kicad Library/3d_models/SOP127P600-8N-SO14.step

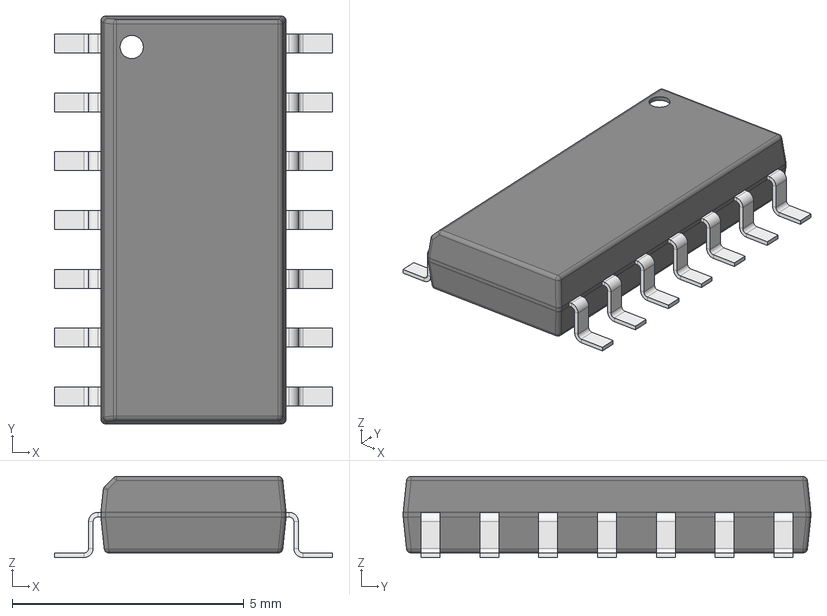
[picture p29: CAD file, 2025-07-21]
Kinben Basic Kicad Library/3d_models/SOP127P600-8N-SO14.step
6.00 x 8.80 x 1.75 mm
Leader x 14
