Kinben-Electronics-Team/Kinben-Unified-Parts-Reference-System/Kinben Basic Kicad Library/3d_models/CAS-220TA1.stp

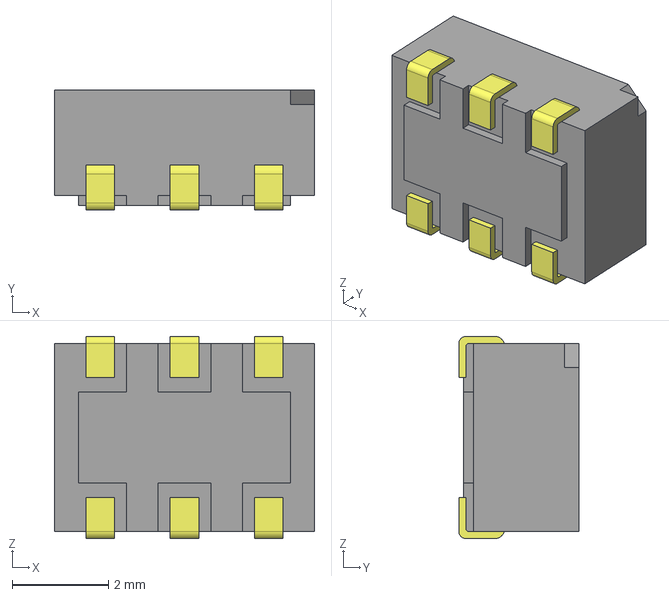
[picture p30: CAD file, 2025-07-21]
Kinben Basic Kicad Library/3d_models/CAS-220TA1.stp
5.40 x 2.50 x 4.20 mm
2 pole_s
CAS_c_22A
