Kinben-Electronics-Team/Kinben-Unified-Parts-Reference-System/Kinben Basic Kicad Library/3d_models/Coilcraft-LPS4018.step

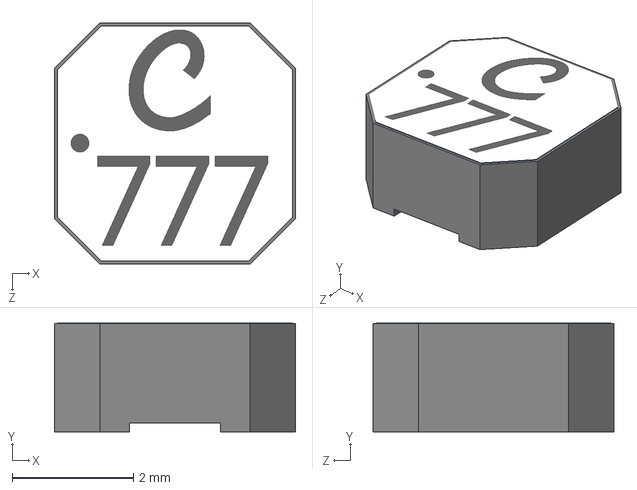
[picture p31: CAD file, 2025-07-21]
Kinben Basic Kicad Library/3d_models/Coilcraft-LPS4018.step
3.98 x 1.80 x 3.98 mm
