Kinben-Electronics-Team/Kinben-Unified-Parts-Reference-System/Kinben Basic Kicad Library/3d_models/2-5S1A.STEP

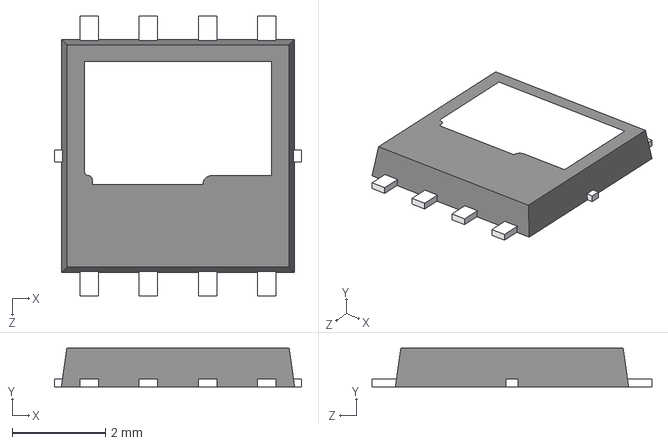
[picture p32: CAD file, 2025-07-21]
Kinben Basic Kicad Library/3d_models/2-5S1A.STEP
5.30 x 0.83 x 6.00 mm
