Kinben-Electronics-Team/Kinben-Unified-Parts-Reference-System/Kinben Basic Kicad Library/3d_models/3220-10-0200.step

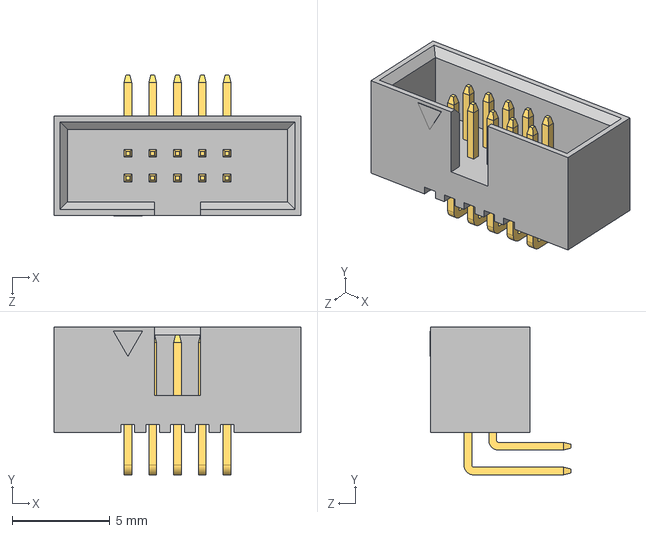
[picture p33: CAD file, 2025-07-21]
Kinben Basic Kicad Library/3d_models/3220-10-0200.step
12.6 x 7.57 x 7.23 mm
00-H
00-T-90
